dohn-joh/keycaps/lever_keycaps/LIMITED_COMPATIBILITY_mx_base.step

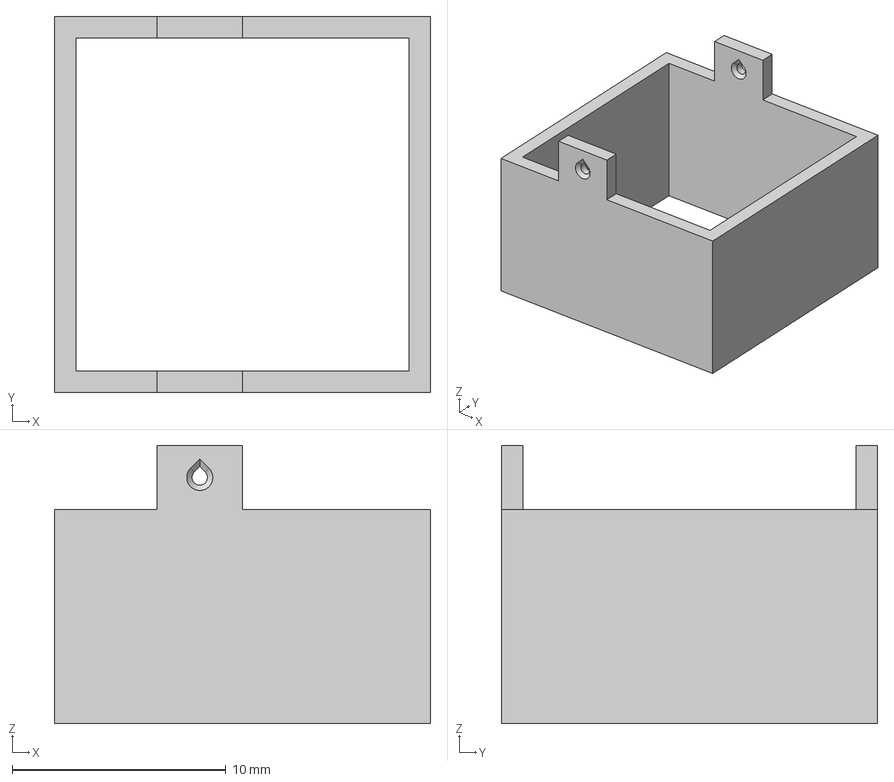
[picture p15: CAD file, 2024-04-04]
lever_keycaps/LIMITED_COMPATIBILITY_mx_base.step
17.6 x 17.6 x 13.0 mm
