dohn-joh/keycaps/lever_keycaps/OLD_choc_base.step

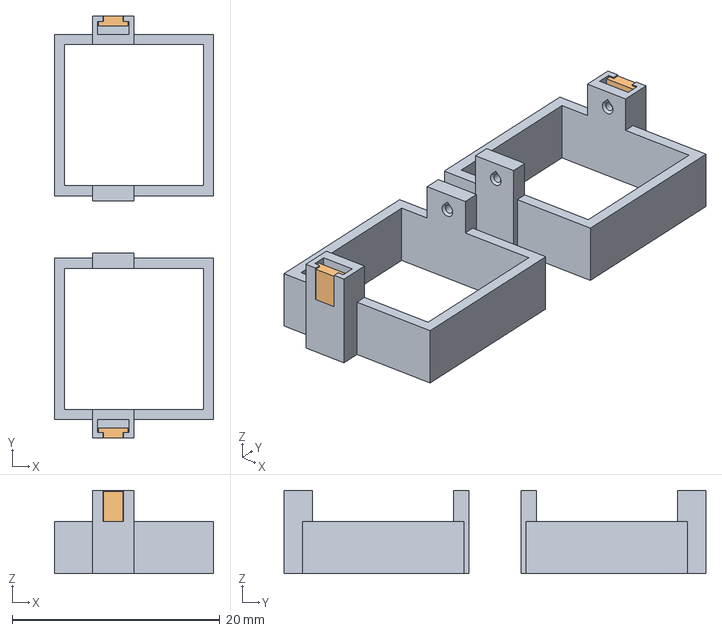
[picture p16: CAD file, 2024-05-17, an earlier design]
lever_keycaps/OLD_choc_base.step
15.3 x 40.6 x 8.00 mm
